ra0sms/picorx_digi/pics/2.jpg

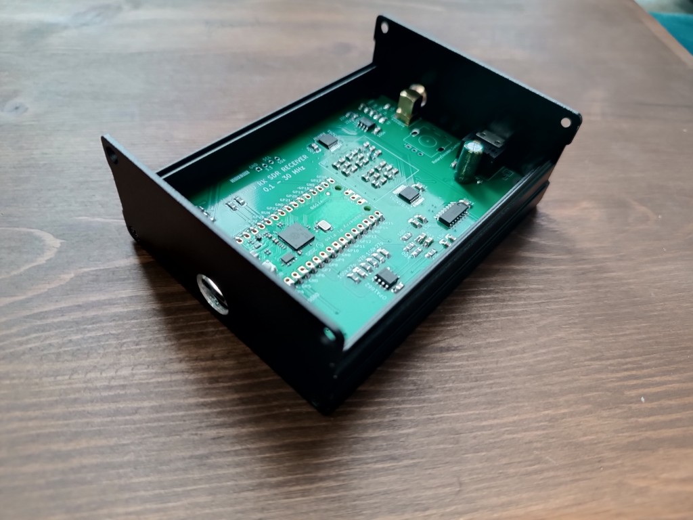
pics/2.jpg
