ra0sms/picorx_digi/pics/3.jpg

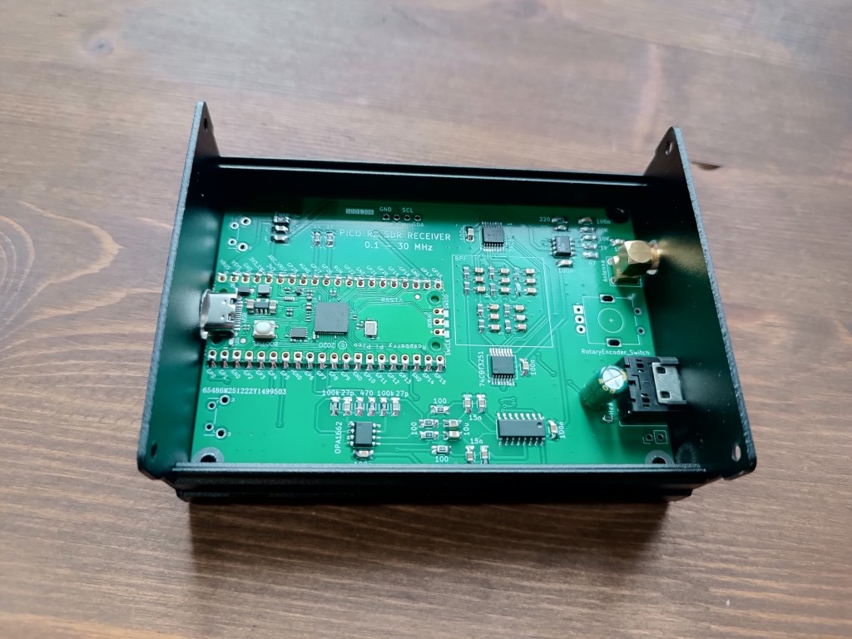
pics/3.jpg
