ra0sms/picorx_digi/pics/4.jpg

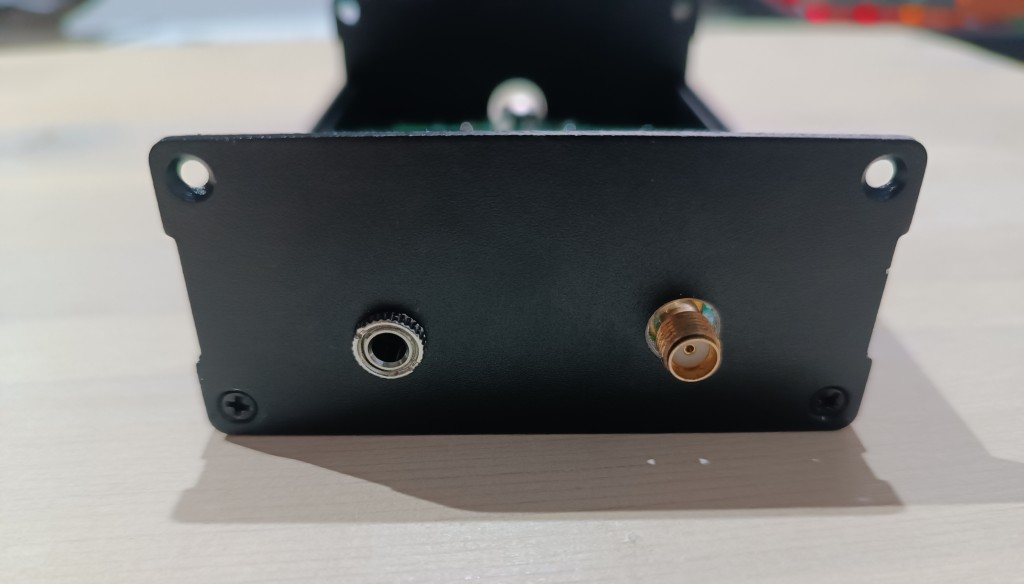
pics/4.jpg
