ra0sms/picorx_digi/pics/5.jpg

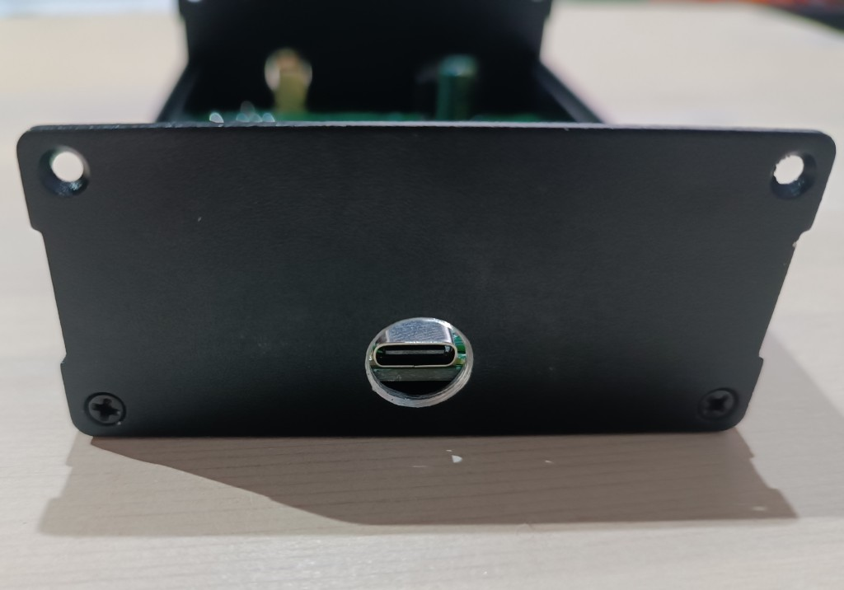
pics/5.jpg
