ra0sms/picorx_digi/pics/6.jpg

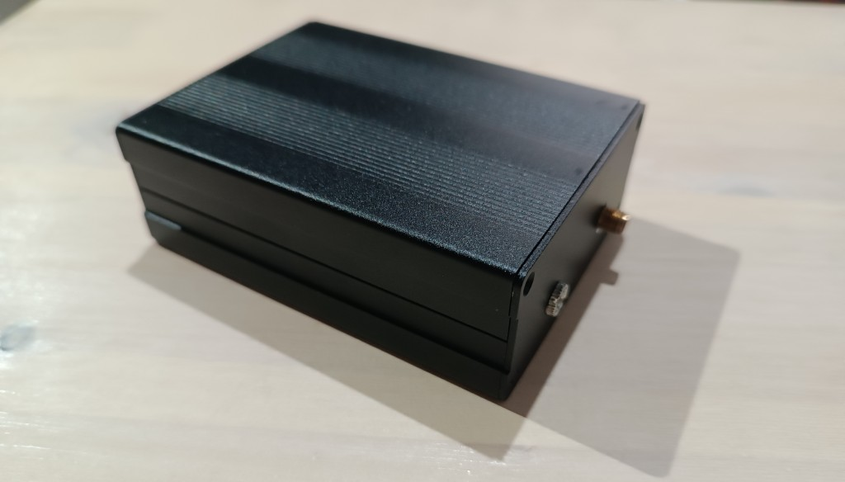
pics/6.jpg
